VogelPapaFinn/MX5-HybridDash/SW/components/lvgl/docs/_static/img/js_calculator.gif

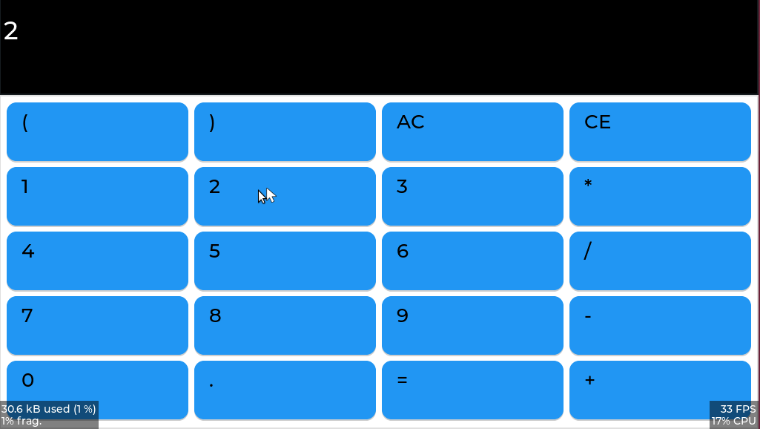
SW/components/lvgl/docs/_static/img/js_calculator.gif
