VogelPapaFinn/MX5-HybridDash/SW/components/lvgl/docs/_static/img/js_code.png

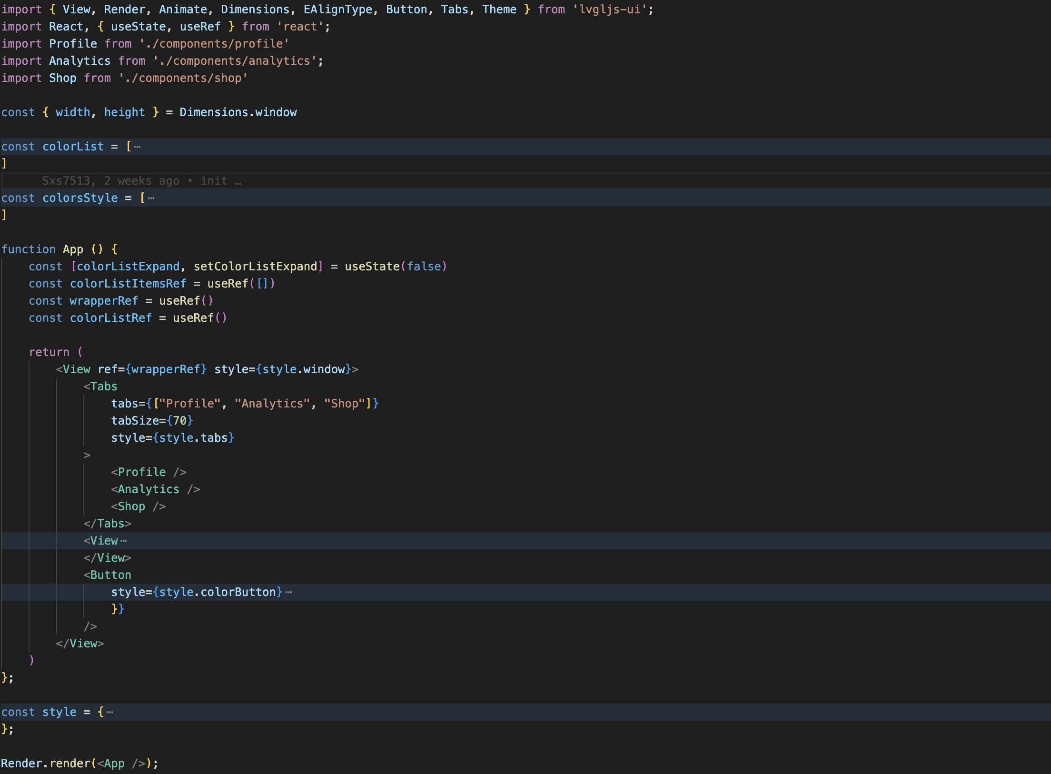
SW/components/lvgl/docs/_static/img/js_code.png
