VogelPapaFinn/MX5-HybridDash/SW/components/lvgl/docs/_static/img/js_on_device.jpg

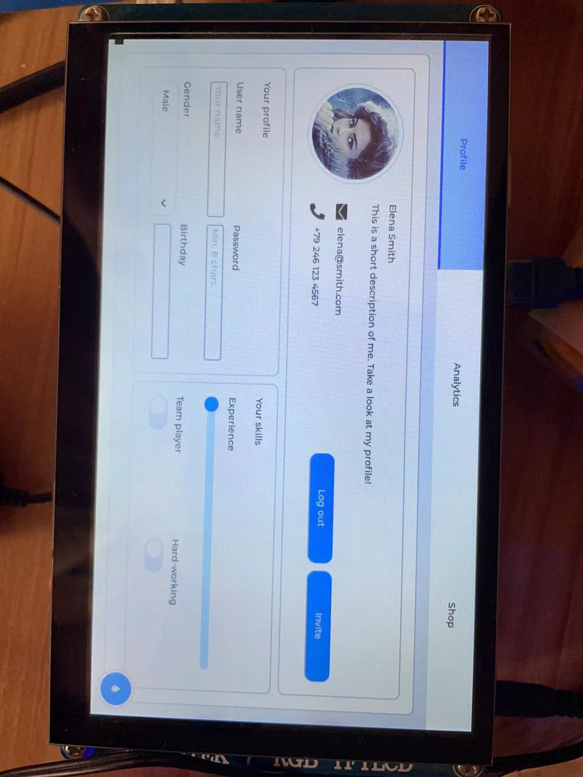
SW/components/lvgl/docs/_static/img/js_on_device.jpg
