VogelPapaFinn/MX5-HybridDash/SW/components/lvgl/docs/_static/img/js_widgets_demo.gif

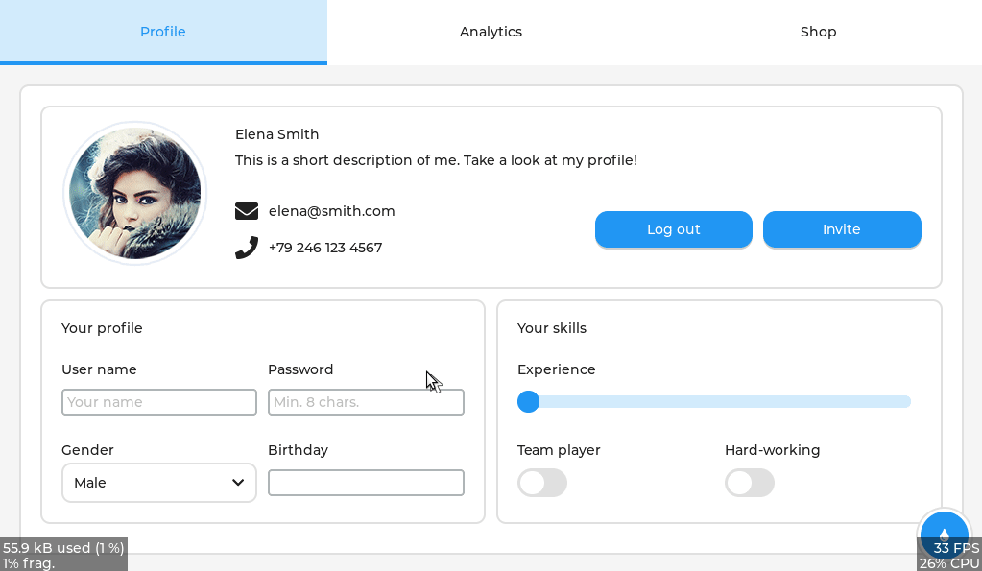
SW/components/lvgl/docs/_static/img/js_widgets_demo.gif
