VogelPapaFinn/MX5-HybridDash/SW/components/lvgl/docs/misc/perfetto_ui.png

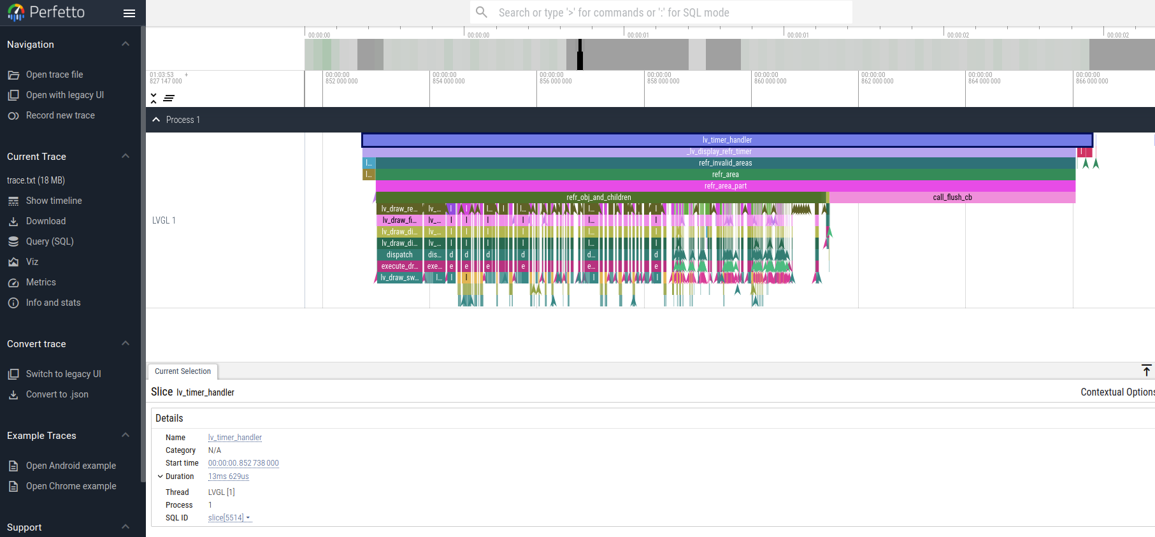
SW/components/lvgl/docs/misc/perfetto_ui.png
