VogelPapaFinn/MX5-HybridDash/SW/components/lvgl/docs/misc/renesas/generate.png

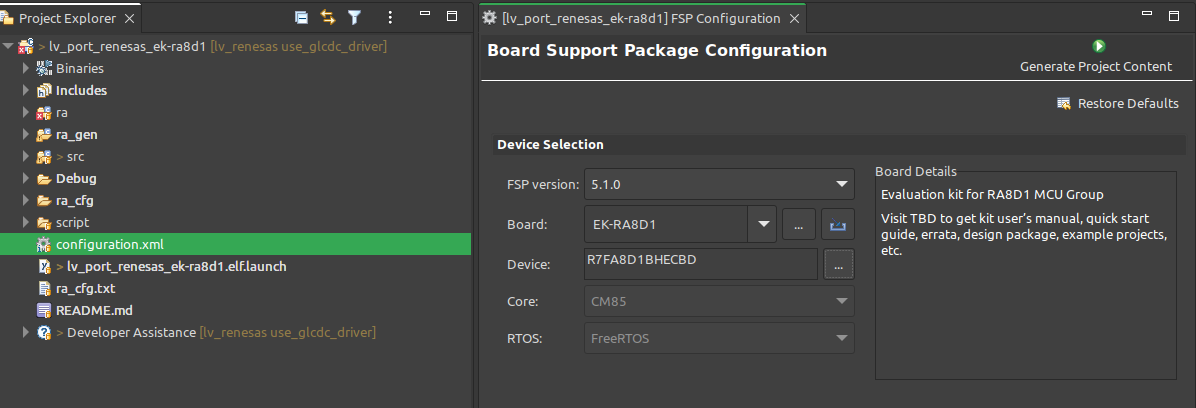
SW/components/lvgl/docs/misc/renesas/generate.png
