VogelPapaFinn/MX5-HybridDash/SW/components/lvgl/docs/misc/renesas/toolchains.png

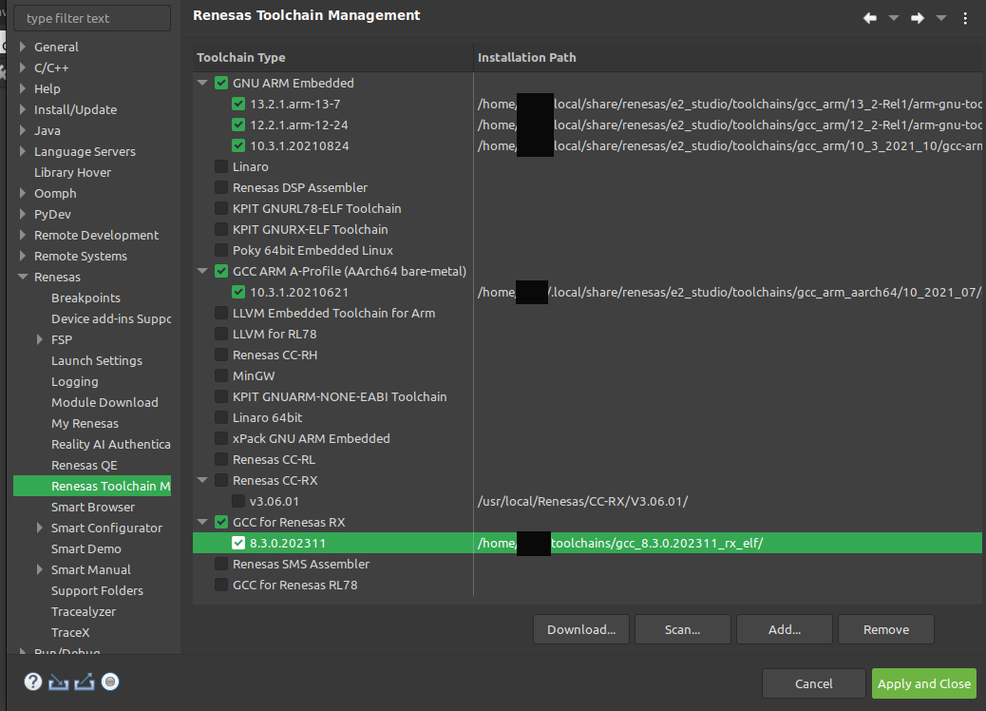
SW/components/lvgl/docs/misc/renesas/toolchains.png
