VogelPapaFinn/MX5-HybridDash/SW/components/lvgl/docs/misc/scale_ticks_on_top.png

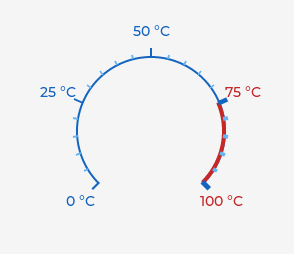
SW/components/lvgl/docs/misc/scale_ticks_on_top.png
