VogelPapaFinn/MX5-HybridDash/HW/3DModels/TPS5430DDAR.step

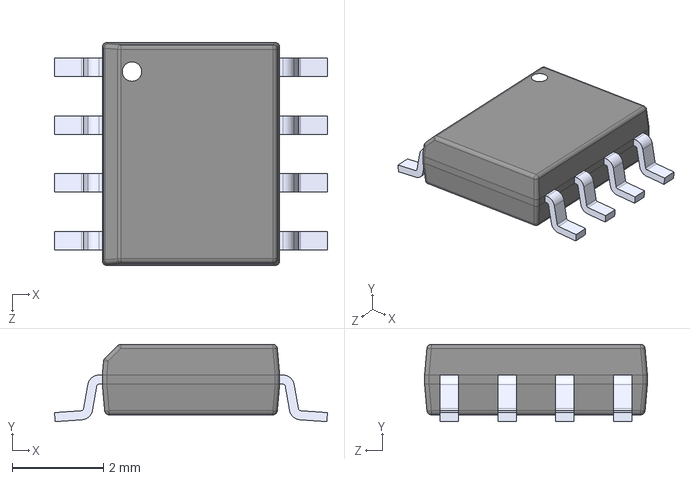
[picture p40: CAD file, 2025-11-15]
HW/3DModels/TPS5430DDAR.step
6.00 x 1.70 x 4.90 mm
