VogelPapaFinn/MX5-HybridDash/HW/3DModels/USB4105-GF-A.step

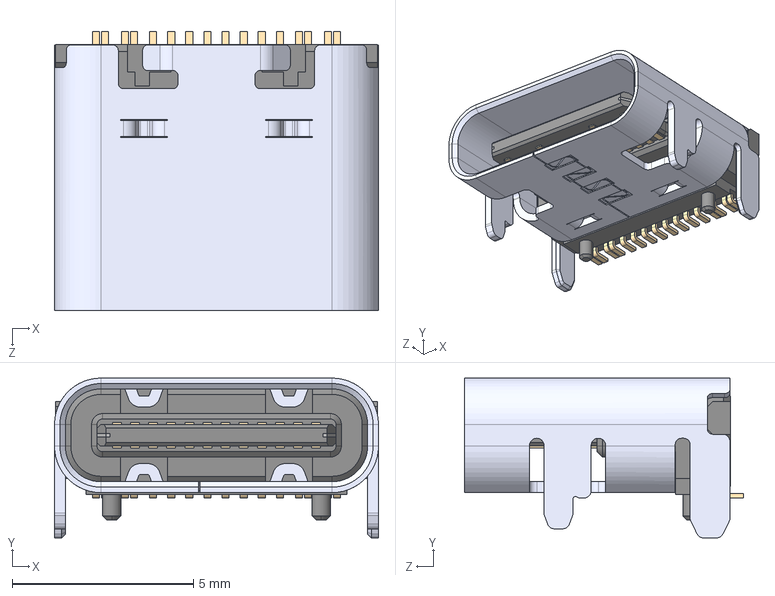
[picture p41: CAD file, 2025-11-15]
HW/3DModels/USB4105-GF-A.step
8.94 x 4.41 x 7.71 mm
