VogelPapaFinn/MX5-HybridDash/SW/components/lvgl/tests/ref_imgs/draw/render/al88/demo_render_border_opa_255.png

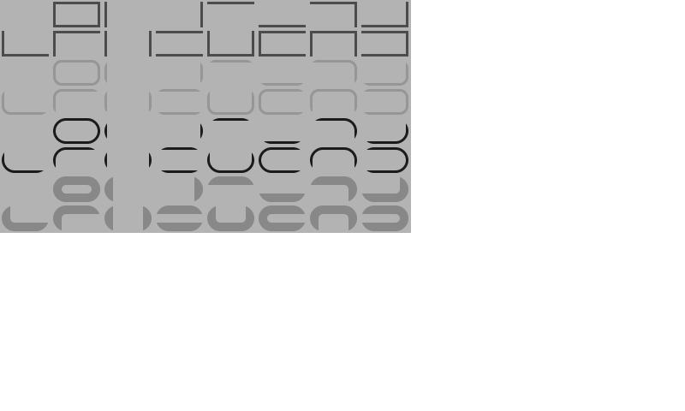
SW/components/lvgl/tests/ref_imgs/draw/render/al88/demo_render_border_opa_255.png
