VogelPapaFinn/MX5-HybridDash/SW/components/lvgl/tests/ref_imgs/draw/render/al88/demo_render_box_shadow_opa_255.png

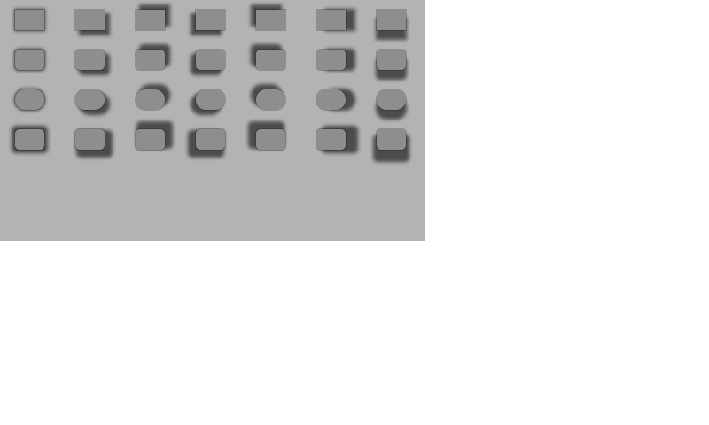
SW/components/lvgl/tests/ref_imgs/draw/render/al88/demo_render_box_shadow_opa_255.png
