VogelPapaFinn/MX5-HybridDash/SW/components/lvgl/tests/ref_imgs/draw/render/al88/demo_render_conical_gradient_opa_128.png

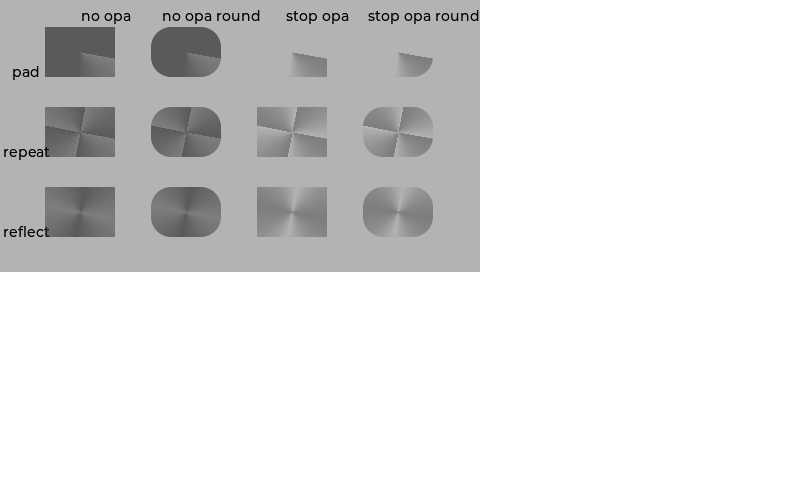
SW/components/lvgl/tests/ref_imgs/draw/render/al88/demo_render_conical_gradient_opa_128.png
