VogelPapaFinn/MX5-HybridDash/SW/components/lvgl/tests/ref_imgs/draw/render/argb8888/demo_render_triangle_opa_128.png

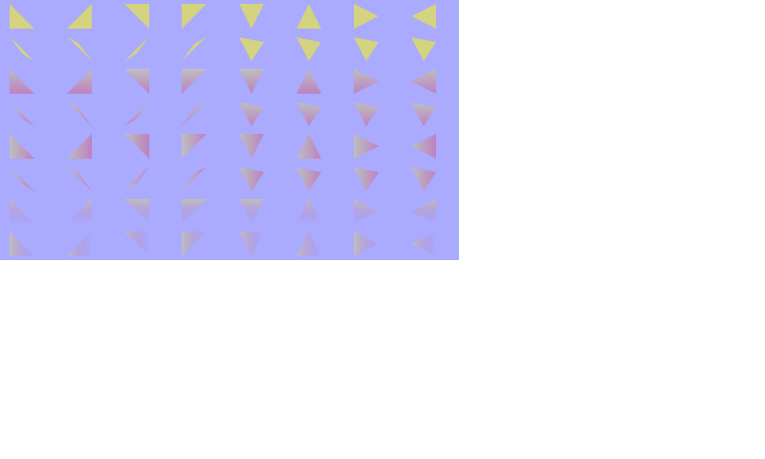
SW/components/lvgl/tests/ref_imgs/draw/render/argb8888/demo_render_triangle_opa_128.png
