VogelPapaFinn/MX5-HybridDash/SW/components/lvgl/tests/ref_imgs/draw/render/i1/demo_render_layer_normal_opa_192.png

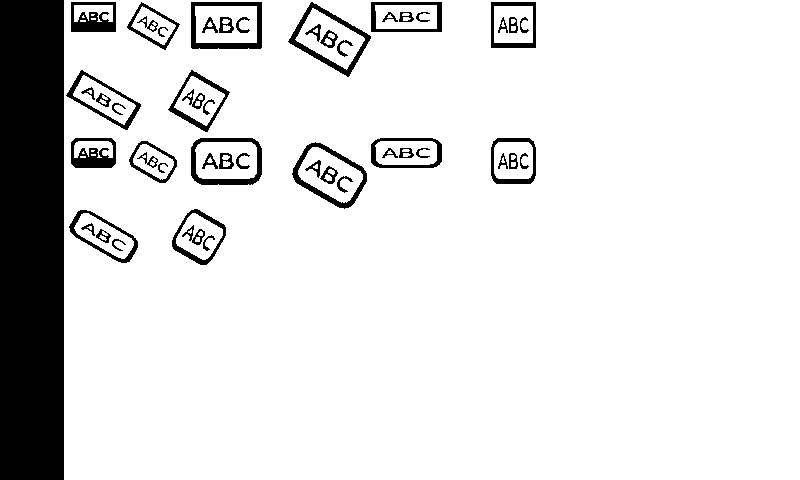
SW/components/lvgl/tests/ref_imgs/draw/render/i1/demo_render_layer_normal_opa_192.png
