VogelPapaFinn/MX5-HybridDash/SW/components/lvgl/tests/ref_imgs/draw/render/i1/demo_render_triangle_opa_255.png

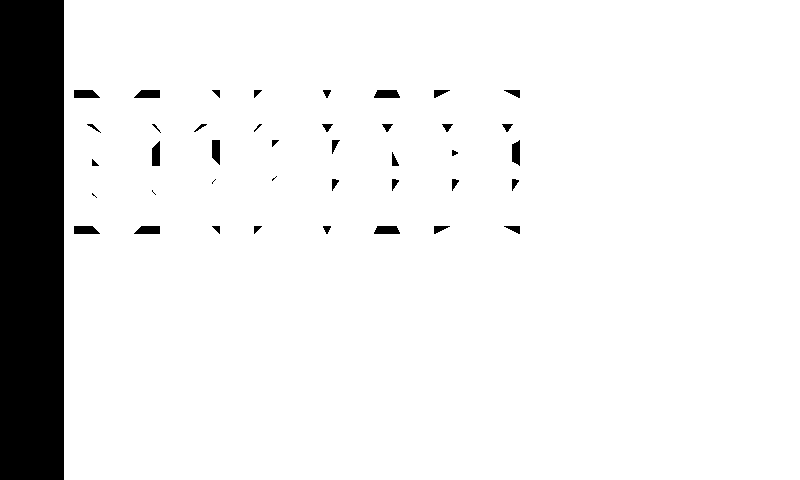
SW/components/lvgl/tests/ref_imgs/draw/render/i1/demo_render_triangle_opa_255.png
