VogelPapaFinn/MX5-HybridDash/SW/components/lvgl/tests/ref_imgs/draw/render/l8/demo_render_arc_normal_opa_128.png

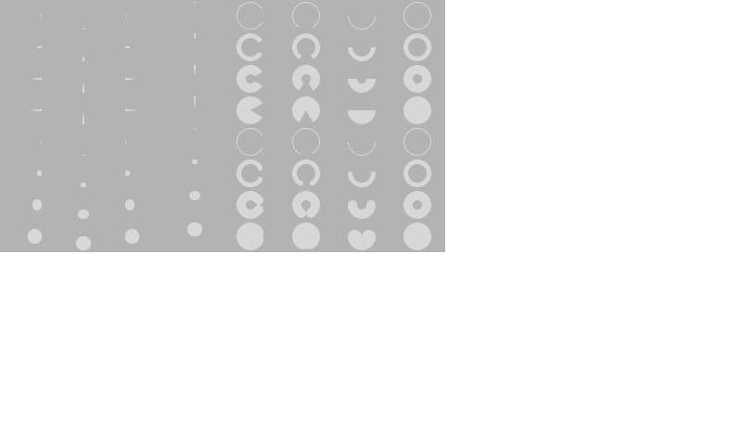
SW/components/lvgl/tests/ref_imgs/draw/render/l8/demo_render_arc_normal_opa_128.png
