VogelPapaFinn/MX5-HybridDash/SW/components/lvgl/tests/ref_imgs/draw/render/xrgb8888/demo_render_line_opa_255.png

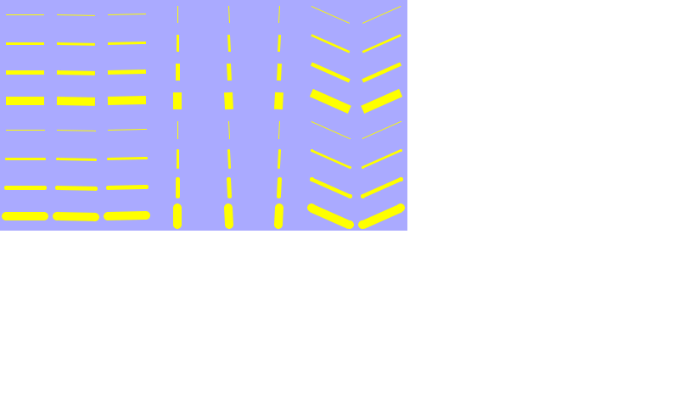
SW/components/lvgl/tests/ref_imgs/draw/render/xrgb8888/demo_render_line_opa_255.png
