VogelPapaFinn/MX5-HybridDash/SW/components/lvgl/tests/ref_imgs_vg_lite/draw/render/rgb888/demo_render_border_opa_255.png

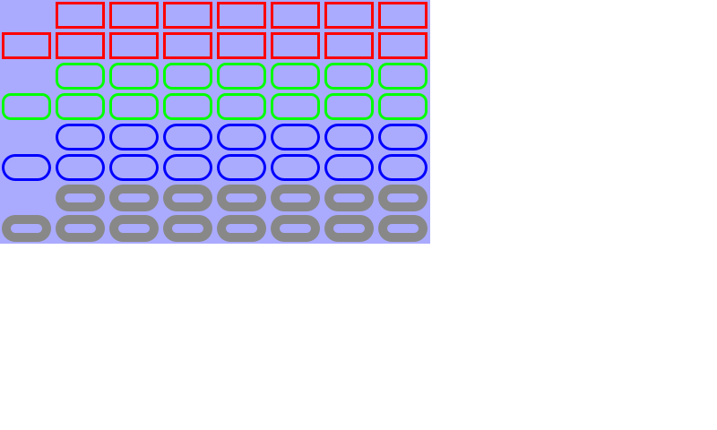
SW/components/lvgl/tests/ref_imgs_vg_lite/draw/render/rgb888/demo_render_border_opa_255.png
